FridayUser/Universal_charger/Zdjęcia/IMG20240525141522.jpg

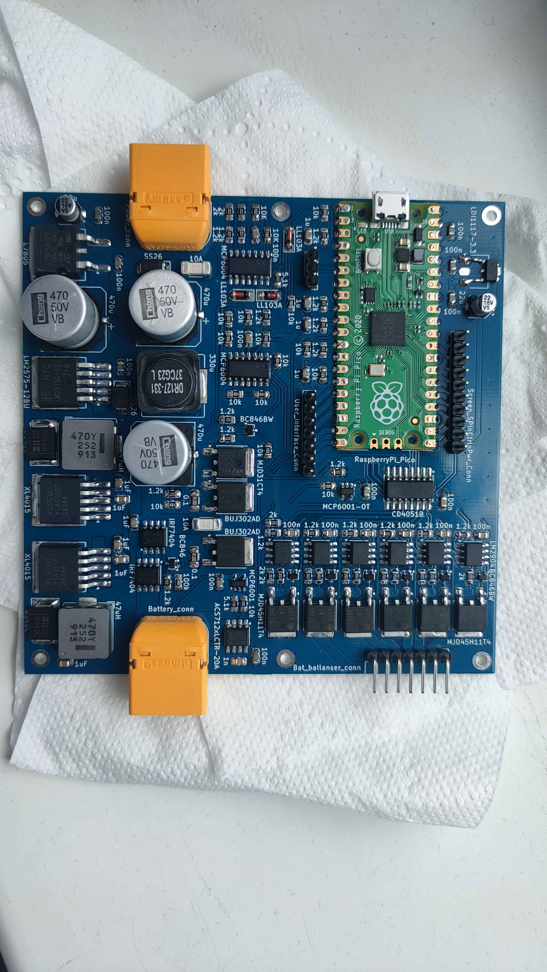
Zdjęcia/IMG20240525141522.jpg
