FridayUser/Universal_charger/Zdjęcia/IMG20240525141531.jpg

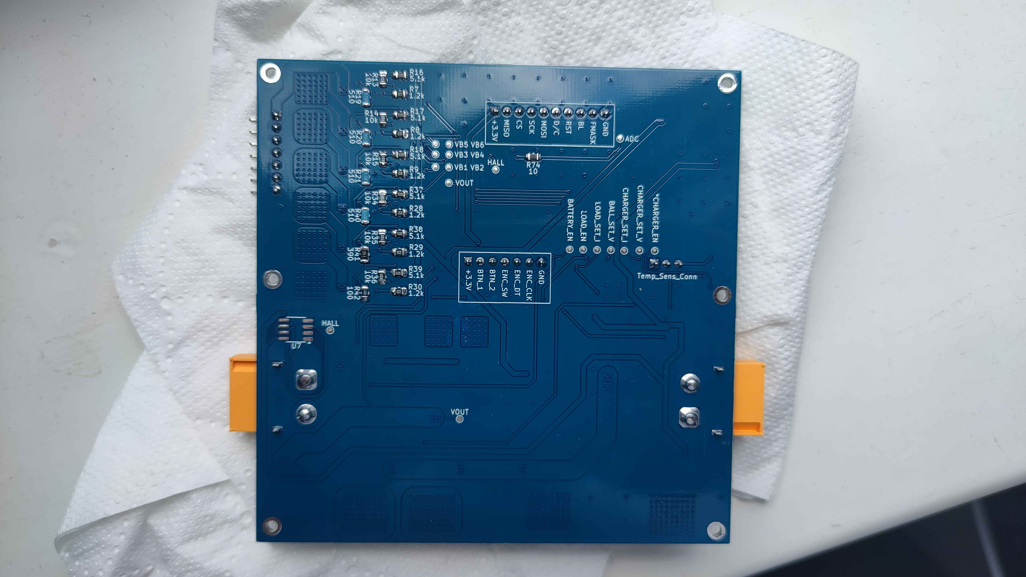
Zdjęcia/IMG20240525141531.jpg
