FridayUser/Universal_charger/Zdjęcia/IMG20240616182940.jpg

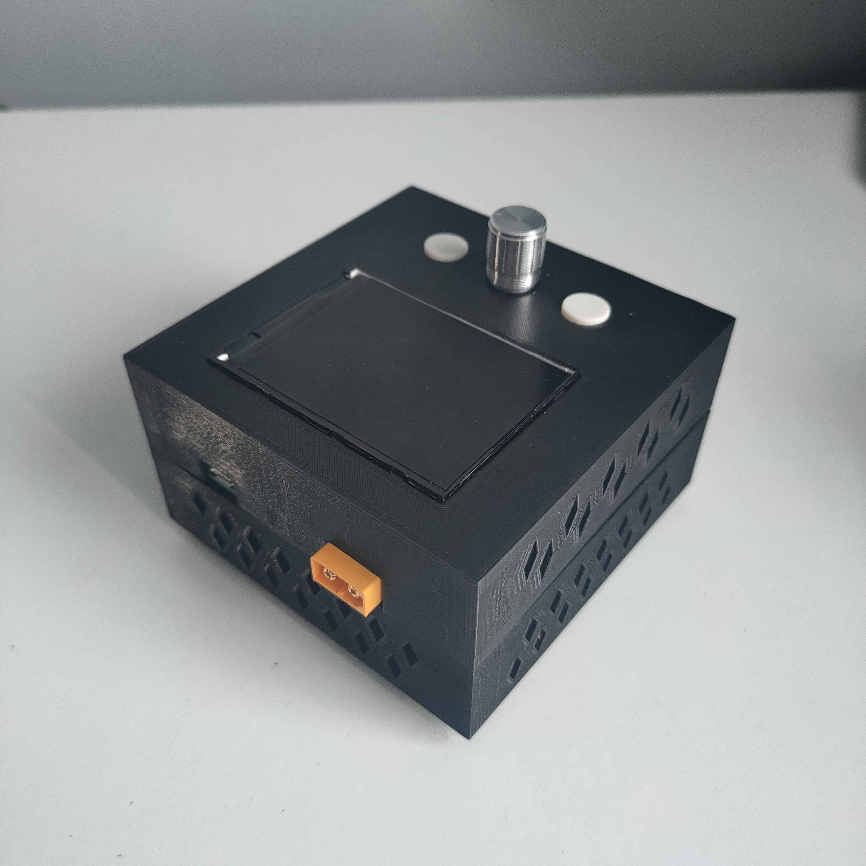
Zdjęcia/IMG20240616182940.jpg
