FridayUser/Universal_charger/Zdjęcia/IMG20240616183134.jpg

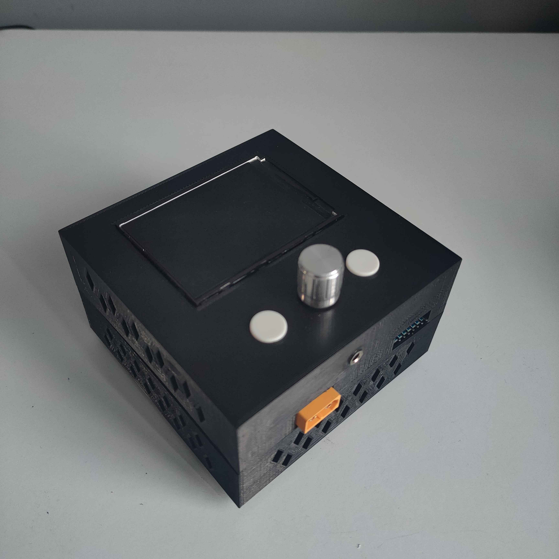
Zdjęcia/IMG20240616183134.jpg
