FridayUser/Universal_charger/Zdjęcia/IMG20240616191806.jpg

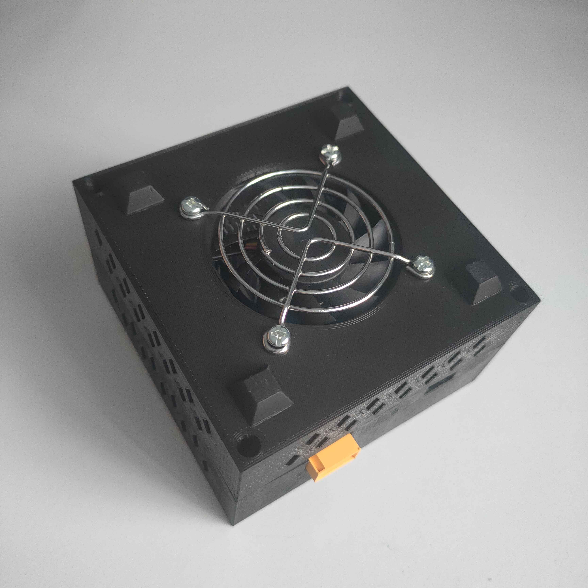
Zdjęcia/IMG20240616191806.jpg
