FridayUser/Universal_charger/LTspice/RC Filter tests.asc

C1: cap; 10µ
R1: res; 2k
V1: voltage; PULSE(0 3.3 0 0 0 0.005m 0.01m)
Named nets: 0, Out
.tran 100m
Fcarrer = 10kHz
R = 1.2k C = 1u      Trise = 7ms Uripple = 62mV
R = 2k    C = 1u      Trise = 10ms Uripple = 37mV
R = 1.2k C = 100n  Trise = 0.5ms Uripple = 625mV
R = 2k    C = 100n  Trise = 1ms Uripple = 380mV
Fcarrer = 100kHz
R = 2k    C = 1u      Trise = 10ms Uripple =3mV
LSB(12b) = 3.3/2^12 = ~0.8mV
LSB(10b) = 3.3/2^10 = ~3mV
Fcarrer = 100kHz
R = 2k    C = 10u      Trise = 90ms Uripple =374uV
Uripple = 10%*LSB
