FridayUser/Universal_charger/LTspice/XL4016_test.asc

CC: cap; 1µ
Cout1: cap; 1000µ
D1: schottky; MBRB2545CT
D2: diode; 1N4148
H1: h; V3; -0.066
L1: ind; 47µ
R1: res; 4k
R2: res; 1k
R3: res; 10k
R8: res; 9k
R9: res; 1k
R_load: res; 2
U1: XL4016
U2: OP07
U3: OP07
V1: voltage; 0.5
V2: voltage; PULSE(0 3.3 10m 1m 1m 9m)
V3: voltage
V4: voltage; 2.5
V_in: voltage; {Vin}
Named nets: 0, in, out, vc, sw, fb
Testing XL4016 EasyEDA LTspice model
8-40V
TTL shutdown
8A
.tran 10m
.param Vin=30
Doesn't work at Vin=8.0V
with ideal components
Input caps not needed
with ideal voltage source
in the simulation
