FridayUser/Universal_charger/LTspice/XL4016_test_I.asc

CC: cap; 1µ
Cout: cap; 1000µ
D1: schottky; MBRB2545CT
H1: h; V3; -0.066
L1: ind; 47µ
R1: res; 9K
R2: res; 1K
R3: res; 2k
R4: res; 2k
R5: res; 2k
R6: res; 2k
R7: res; 1k
R8: res; 0.6k
R9: res; 4.3k
R10: res; 820
R11: res; 5k
R12: res; 10k
R13: res; 10k
R14: res; 5k
R_load: res; 10
U1: XL4016
U2: UniversalOpAmp
U3: UniversalOpAmp
U4: OP07
U5: OP284
V1: voltage; 30
V2: voltage; 1.5
V3: voltage
V4: voltage; 5
V5: voltage; 3.3
V6: voltage
V7: voltage; 1.65
Named nets: 0, in, out, vc, sw, fb, ref, vp, 12v
Testing XL4016 EasyEDA LTspice model
8A
.tran 10m
with ideal components
Second output cap not needed
in the simulation, because of
 ideal 1000uF cap
;.step param vp list 2.7 2.4 2.1 1.8 1.5 1.2 0.9
