FridayUser/Universal_charger/LTspice/battery_switch.asc

M1: nmos; BSB012N03LX3
M2: nmos; BSB012N03LX3
M3: pmos; IRF7404
M4: pmos; IRF7404
M5: pmos; FDS4435A
M6: pmos; FDS4435A
Q1: npn; BC547B
Q2: npn; BC547B
R1: res; 1
R2: res; 20
R3: res; 100k
R4: res; 1k
R5: res; 10
R6: res; 100k
R7: res; 1k
V1: voltage; 20
V2: voltage; 3.3
V3: voltage; 20
V4: voltage; 20
V5: voltage; 3.3
V6: voltage; 3.3
Named nets: 0
.tran 1
