FridayUser/Universal_charger/LTspice/potwornica.asc

CC1: cap; 1µ
CC2: cap; 1µ
CC: cap; 1µ
Cout: cap; 1000µ
D1: schottky; MBRB2545CT
D2: diode
D3: diode
D4: schottky; MBRB2545CT
D5: schottky; MBRB2545CT
H1: h; V3; -0.066
L1: ind; 47µ
L2: ind; 47µ
R1: res; 9K
R2: res; 1K
R9: res; 10k
R11: res; 3.4k
R12: res; 10k
R13: res; 10k
R14: res; 3.4k
R_load: res; 1
U1: XL4016
U2: UniversalOpAmp
U3: UniversalOpAmp
U4: OP07
U5: OP07
U6: XL4016
U7: XL4016
V1: voltage; 30
V2: voltage; 1.8
V3: voltage
V4: voltage; 3.3
V5: voltage; 5
V6: voltage; 12
V7: voltage; 1.65
Named nets: 0, in, out, vc, sw, fb, ref, 12v
8A
.tran 10m
Second output cap not needed
in the simulation, because of
 ideal 1000uF cap
;.step param vp list 2.7 2.4 2.1 1.8 1.5 1.2 0.9
