FridayUser/Universal_charger/LTspice/pomiar_Rw.asc

H1: h; V1; -0.1
Q1: npn; 2N3055
Q2: npn; 2N2222
Q3: npn; BC547B
Q4: npn; 2N3055
R1: res; 10k
R2: res; 5.1k
R3: res; 10k
R4: res; 0.1
R5: res; 1.2k
R6: res; 1.2k
R7: res; 1.2k
R8: res; 15k
R9: res; 10k
R10: res; 10k
R11: res; 10k
R12: res; 10k
R13: res; 10k
R14: res; 10k
R15: res; 0.1
U1: UniversalOpAmp
U3: UniversalOpAmp
U4: UniversalOpAmp
U5: OP07
U6: OP07
V1: voltage; 22; Rser=0.1
V2: voltage; 1
V3: voltage; 5
V4: voltage; 2.5v
V5: voltage; 3.3
Named nets: 0, 12v
.tran 0 10m 0
hall sensor
max 10W
Uce min 30v
Ic min 800ma
Pmax=250W 1s
Uce= min 30V
Ic = 10A
Uwy=I*0.1
Enable
set I (0-5)
