FridayUser/Universal_charger/LTspice/NiMh.asc

D1: zener; 1v4
I1: current; PWL(0 -10m 10m {2.5*n})
V1: cell; NH15-2.5
Named nets: 0, 1
.model 1v4 d(Vrev=1.4)
.step param n list 2 1 .5 .2 .1
.tran 0 {3600/n} 0 {3600*5m/n}
.subckt NH15-2.5 A K
C1 A K 15m Rser=18m ; ac impedance
R1 A 1 R=tbl(V(1,K),1,150m,1.1,70m,1.2,50m,1.26,40m,1.27,30m)
C2 1 K Q=tbl(x,0,0,1.1,108,1.2,1k08,1.26,3k6,1.27,7k2,1.34,8k64,1.4,9k)
D1 K 1 1v5 ; self discharge, reverse and over voltages
.model 1v5 d(Vrev=1.5 Ron=0.1 Roff=1k2)
.ends NH15-2.5
To see discharge curves in hours, 
left mouse click on time axis and
edit from "time" to "time/3600s"
ENERGIZER NH15-2500 Nickel-Metal Hydride 1.2V 2.5AHr AA Rechargeable Cell Subcircuit
November 2007 by analogspiceman
For product engineering data sheet see:
http://data.energizer.com/PDFs/nh15-2500.pdf
